DavidCBarrett/APRemote/data/android-chrome-192x192.png

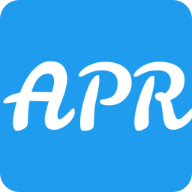
data/android-chrome-192x192.png
